calvin-mcd/peanut/Images/IMG_4146.jpg

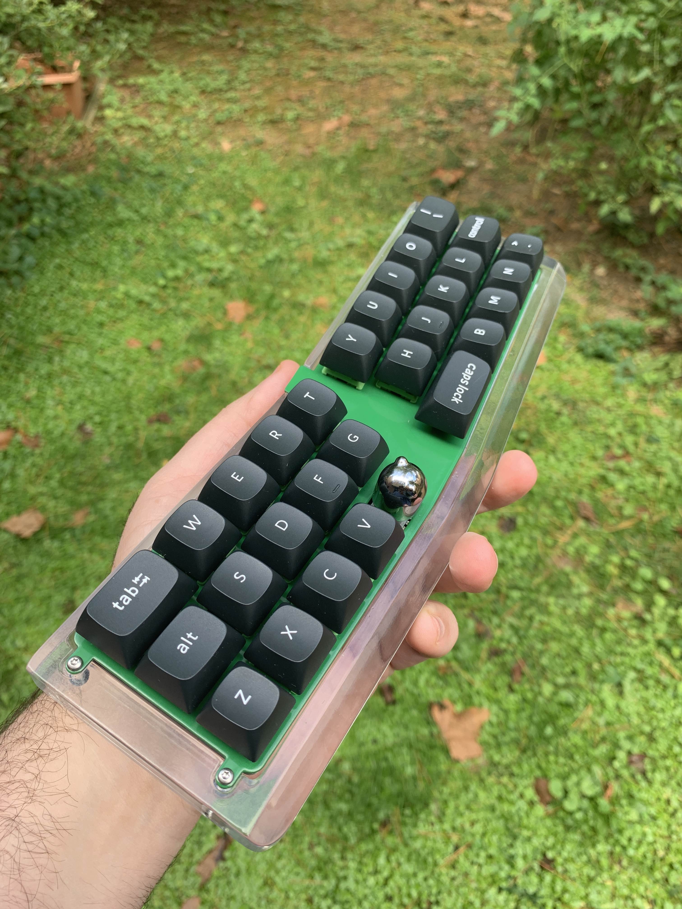
Images/IMG_4146.jpg
