calvin-mcd/peanut/Firmware/Source Code/keymaps/vial/config.h

#pragma once

#define VIAL_KEYBOARD_UID {0x8E, 0x1C, 0xDC, 0x7C, 0x18, 0x59, 0x9E, 0x26}

#define VIAL_UNLOCK_COMBO_ROWS { 0, 0 }
#define VIAL_UNLOCK_COMBO_COLS { 0, 9 }

#define VIAL_COMBO_ENTRIES 69
#define DYNAMIC_KEYMAP_LAYER_COUNT 6
